egazzarr/head-md-AI-family/process/02-24-brainstorming_with_family1.jpeg

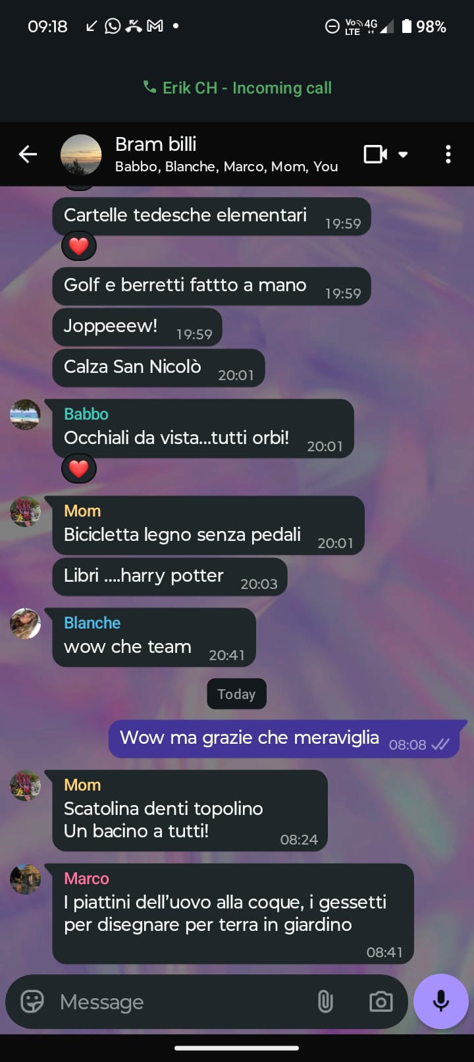
process/02-24-brainstorming_with_family1.jpeg
