egazzarr/head-md-AI-family/process/02-25 - authoritative table.jpeg

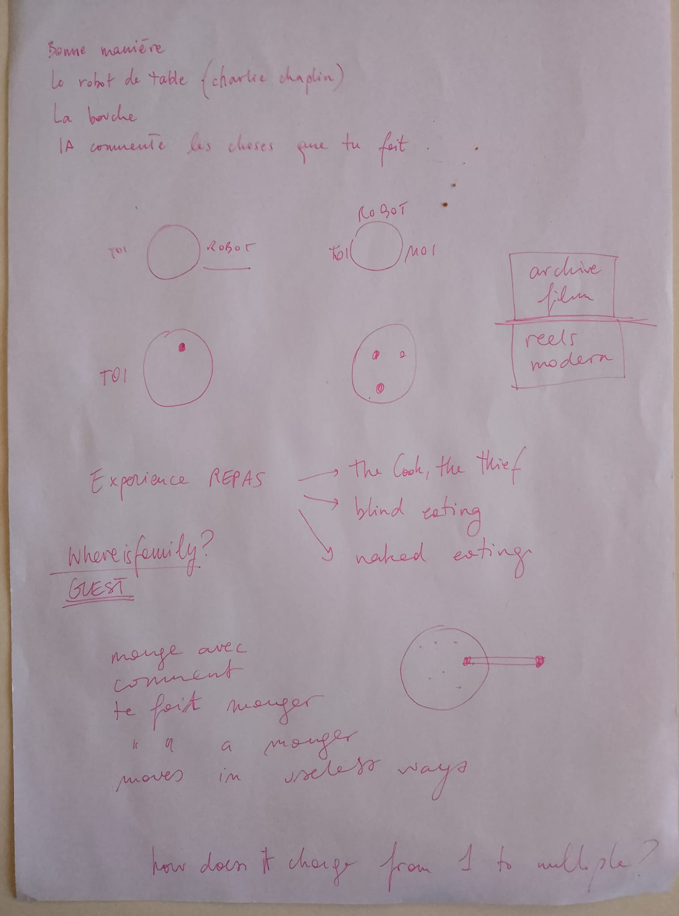
process/02-25 - authoritative table.jpeg
