egazzarr/head-md-AI-family/process/02-27-process.jpeg

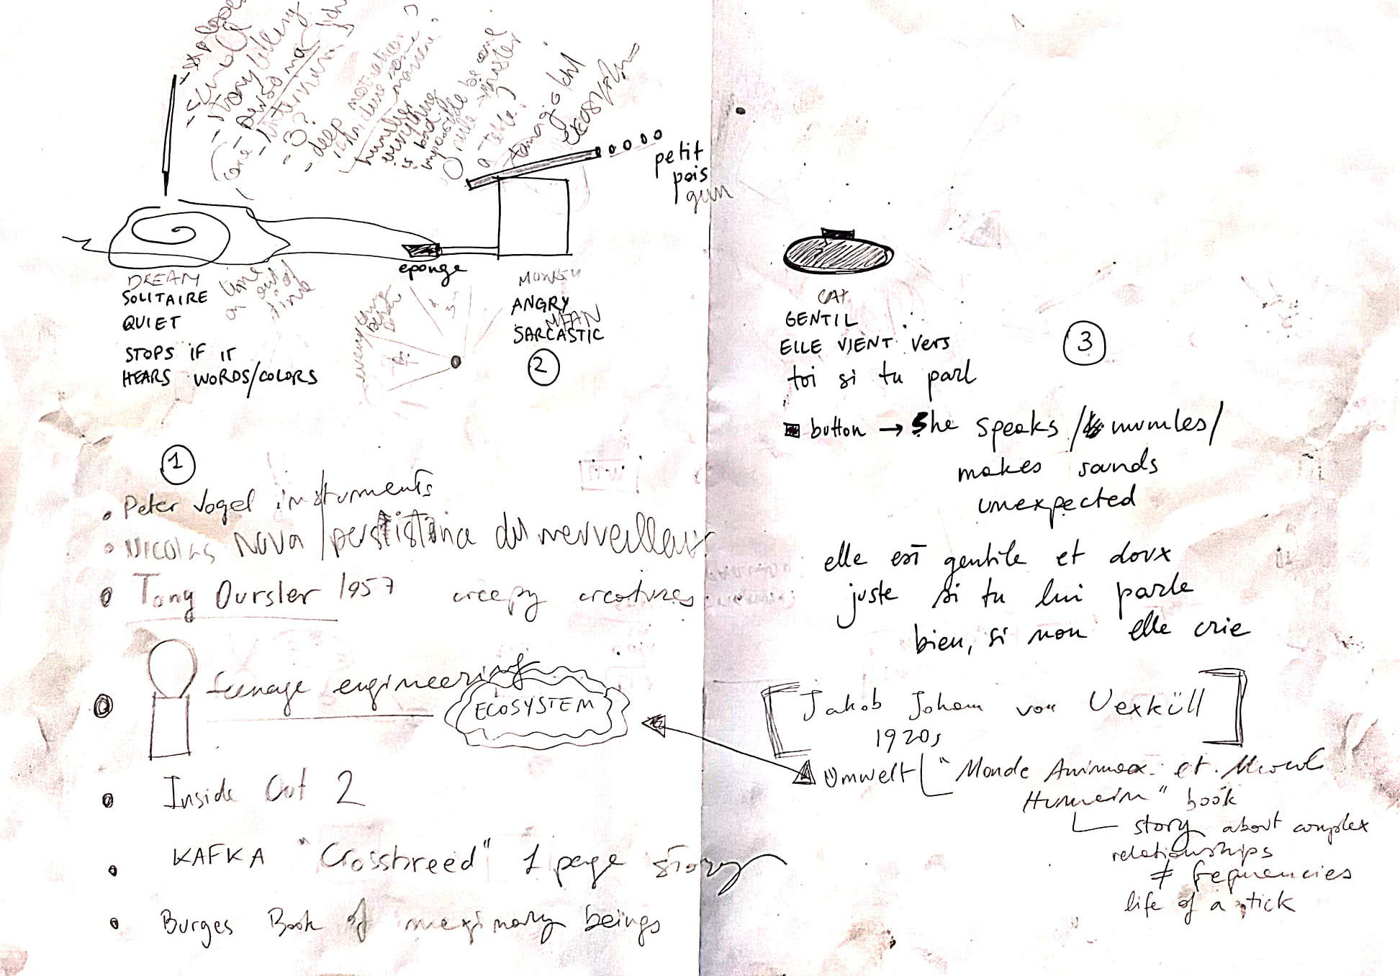
process/02-27-process.jpeg
