egazzarr/head-md-AI-family/process/WhatsApp Image 2026-03-05 at 17.39.34(3).jpeg

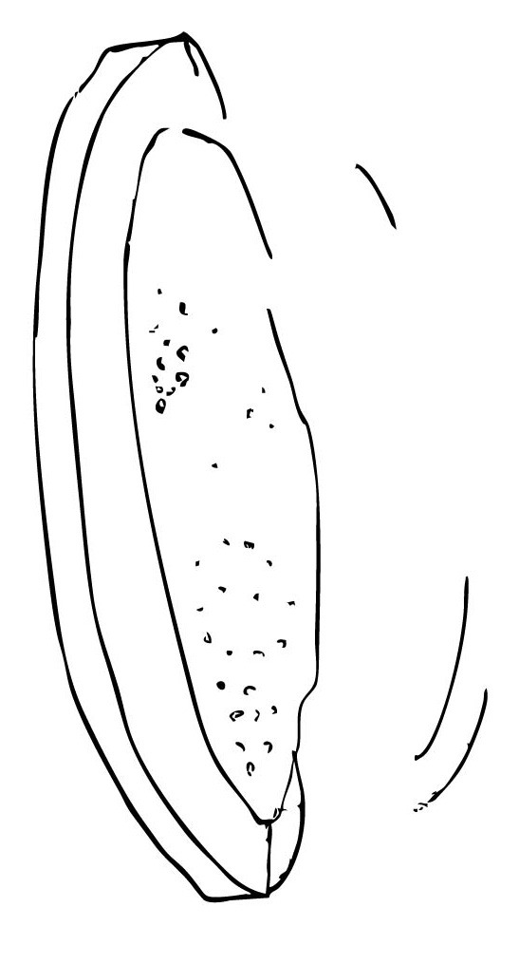
process/WhatsApp Image 2026-03-05 at 17.39.34(3).jpeg
