egazzarr/head-md-AI-family/references/02-25.jpeg

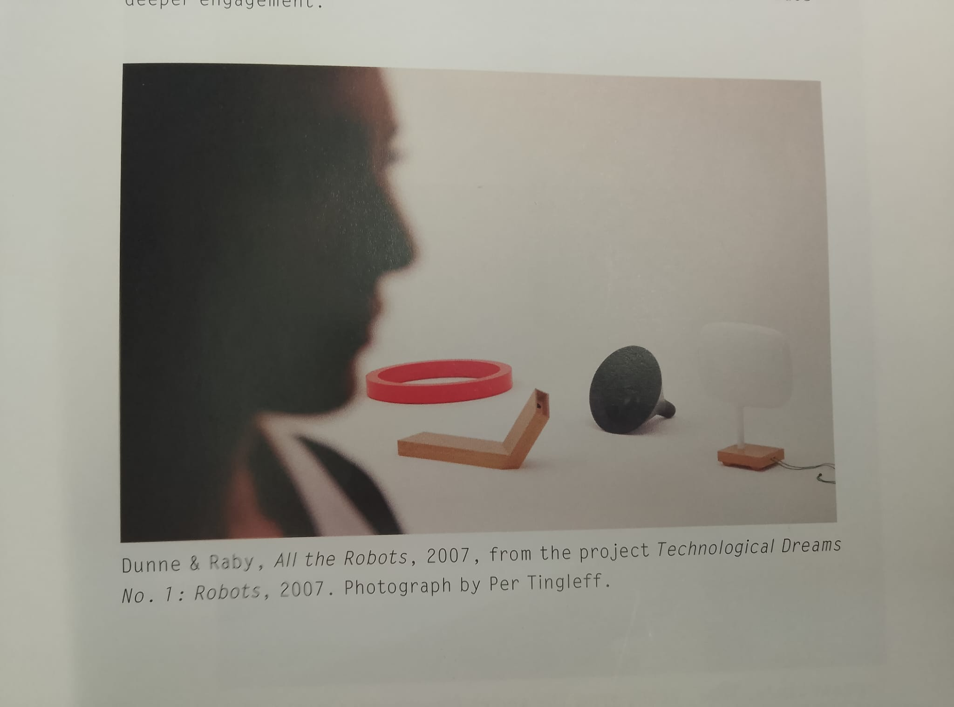
references/02-25.jpeg
