egazzarr/head-md-AI-family/references/carlthechair.jpeg

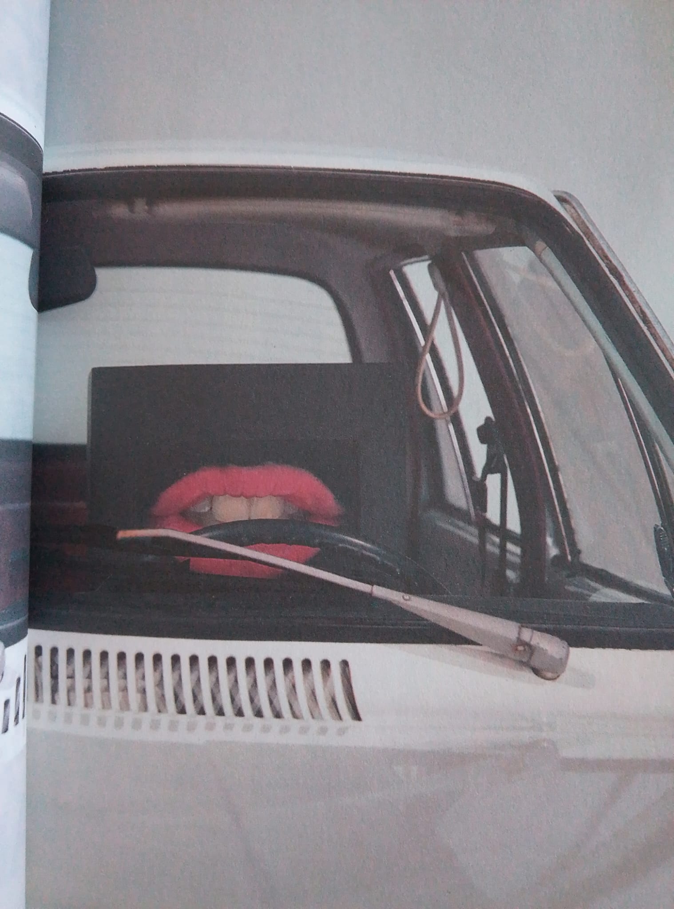
references/carlthechair.jpeg
