egazzarr/head-md-AI-family/references/chaplin.png

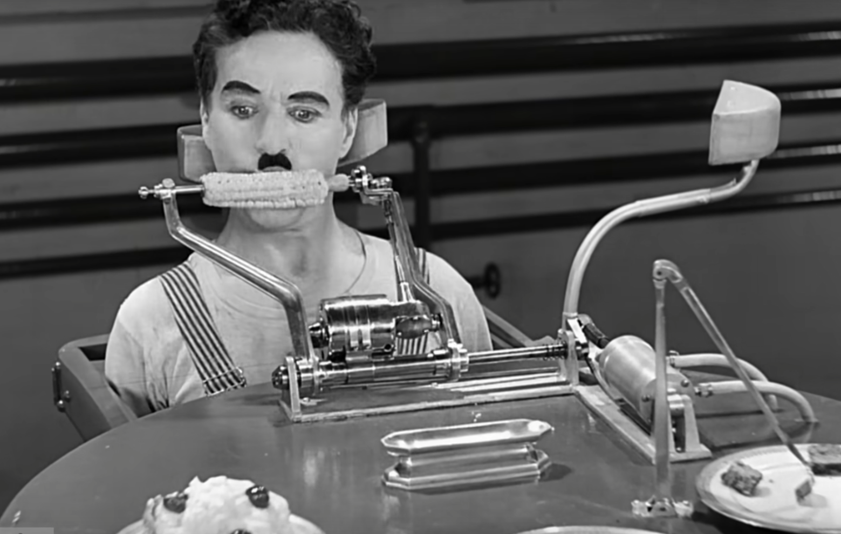
references/chaplin.png
