egazzarr/head-md-AI-family/references/esme.jpeg

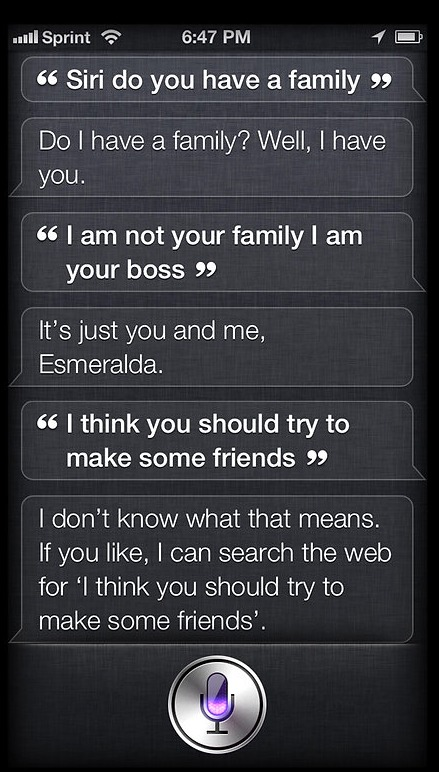
references/esme.jpeg
