egazzarr/head-md-AI-family/references/Fanny-and-Alexander-1982-8.jpg

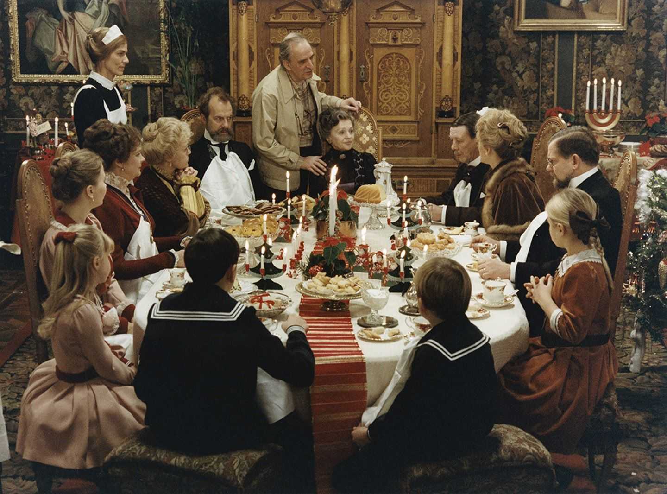
references/Fanny-and-Alexander-1982-8.jpg
