egazzarr/head-md-AI-family/references/friends electric.jpg

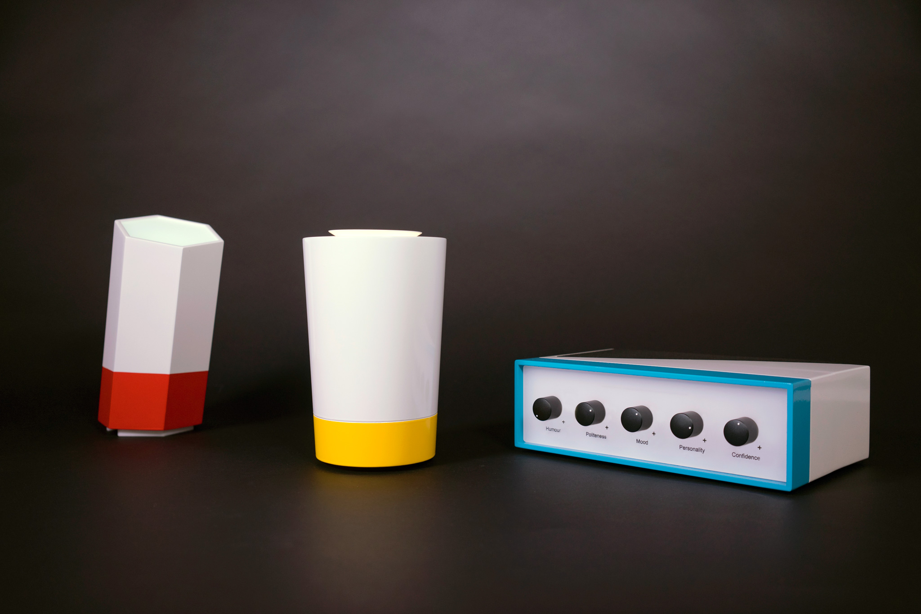
references/friends electric.jpg
