egazzarr/head-md-AI-family/references/impossible1.jpeg

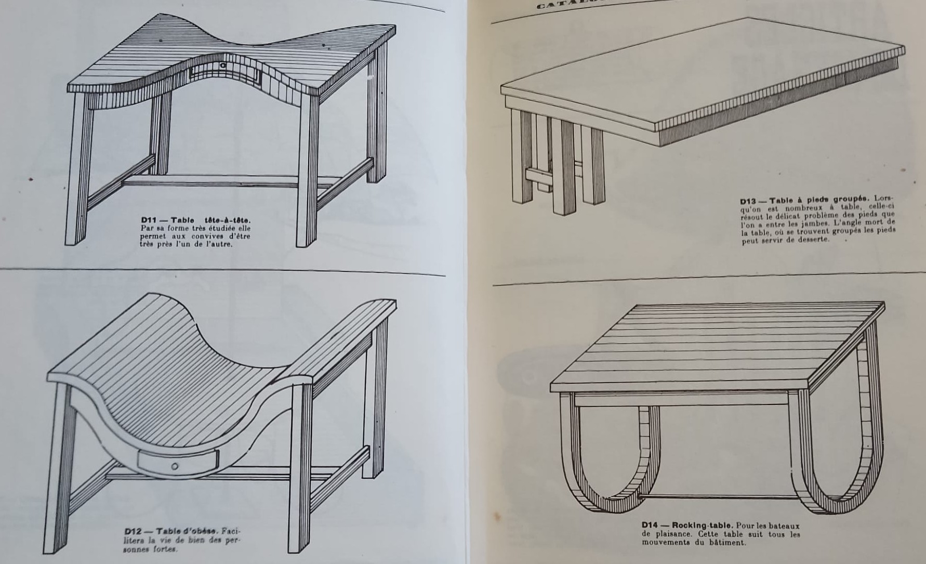
references/impossible1.jpeg
