egazzarr/head-md-AI-family/references/lisa.jpeg

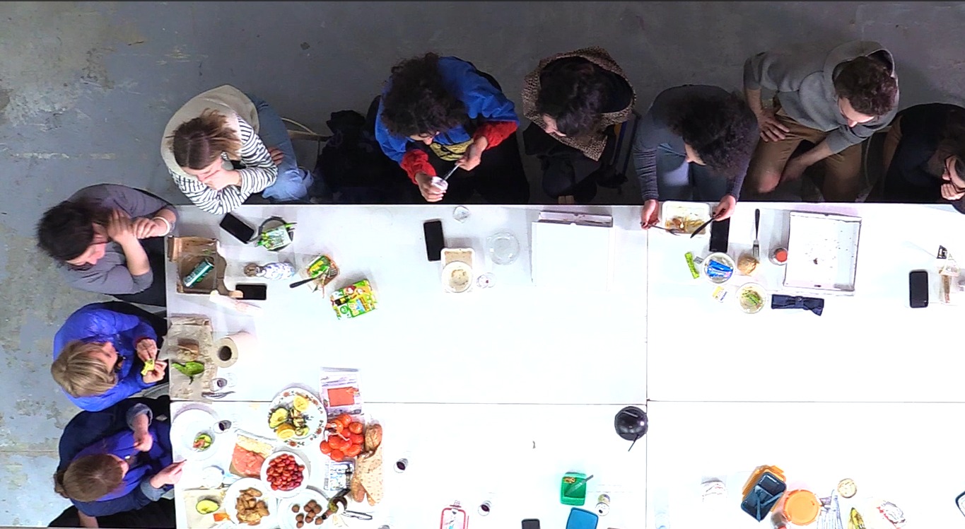
references/lisa.jpeg
