egazzarr/head-md-AI-family/references/sedie.jpeg

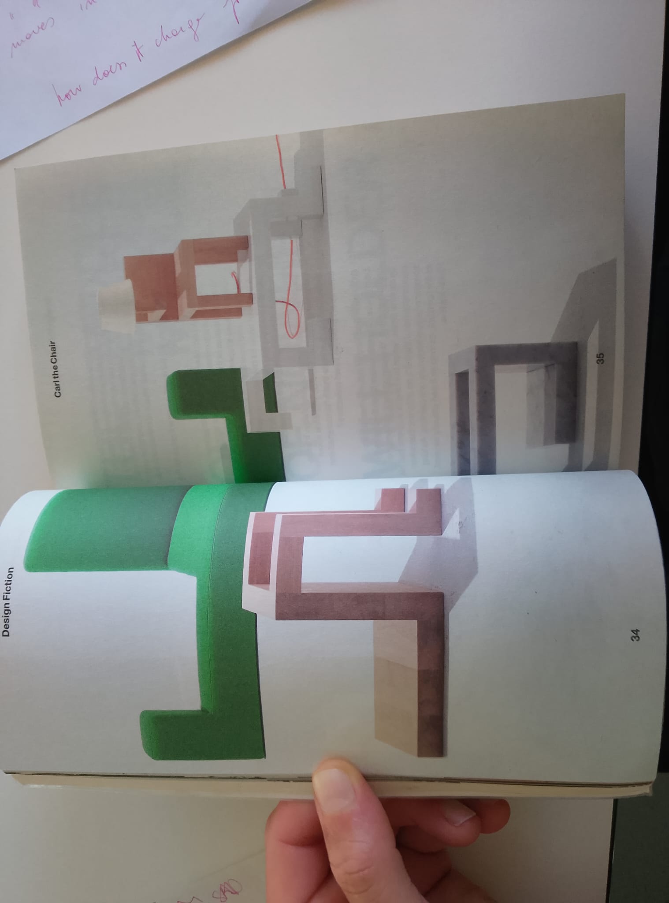
references/sedie.jpeg
