egazzarr/head-md-AI-family/references/tati.png

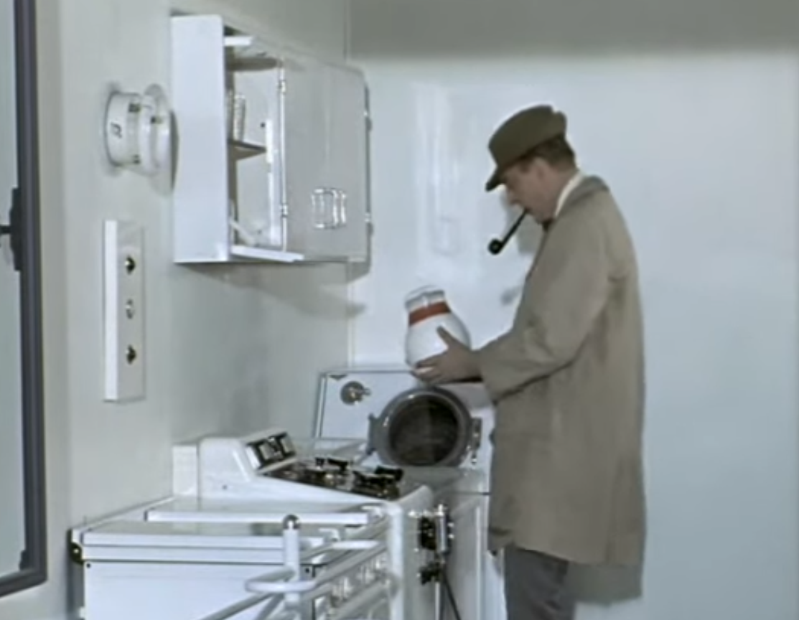
references/tati.png
