egazzarr/head-md-AI-family/references/The-Cook-The-Thief-Still-3-1-1024x435.jpg

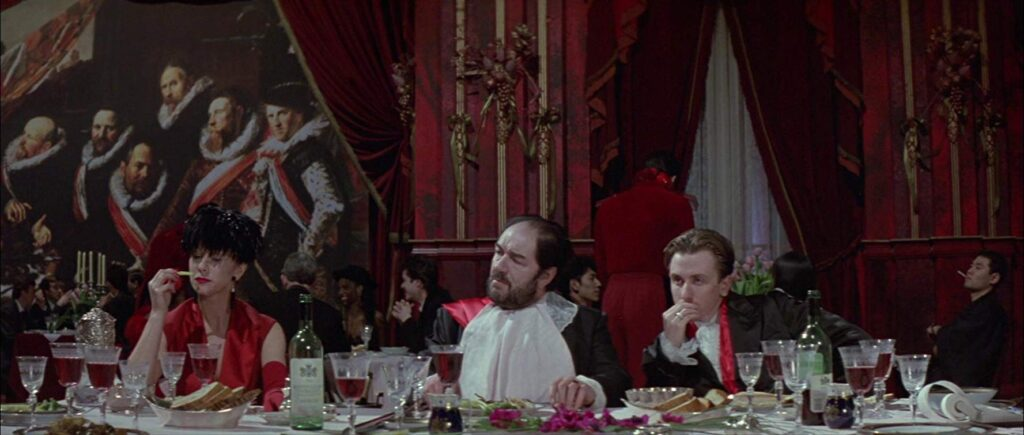
references/The-Cook-The-Thief-Still-3-1-1024x435.jpg
