egazzarr/head-md-AI-family/FamilyDinnerFINALSETUP.jpeg

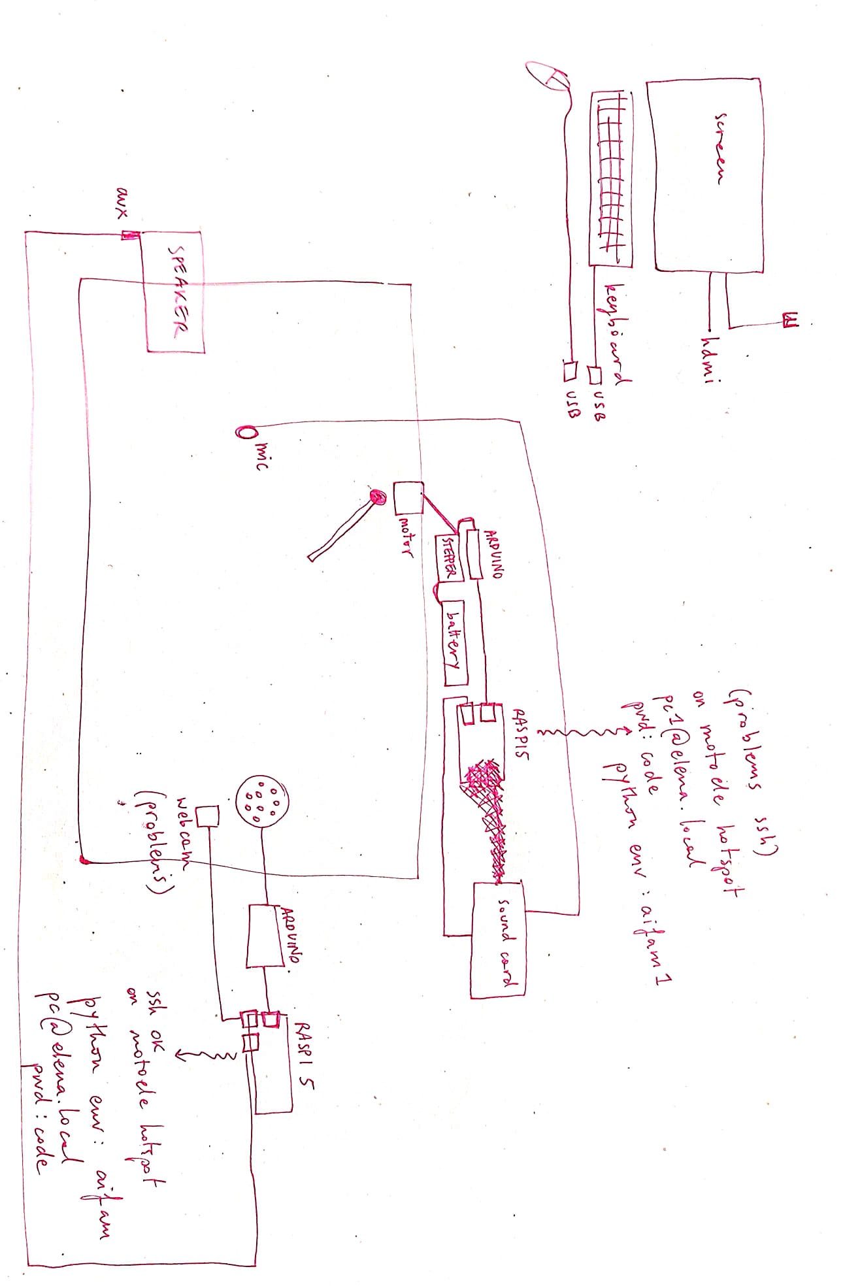
FamilyDinnerFINALSETUP.jpeg
